riezky-gitH/OtoPonic/Dokumentasi/WhatsApp Image 2025-06-03 at 14.11.09_1a706787.jpg

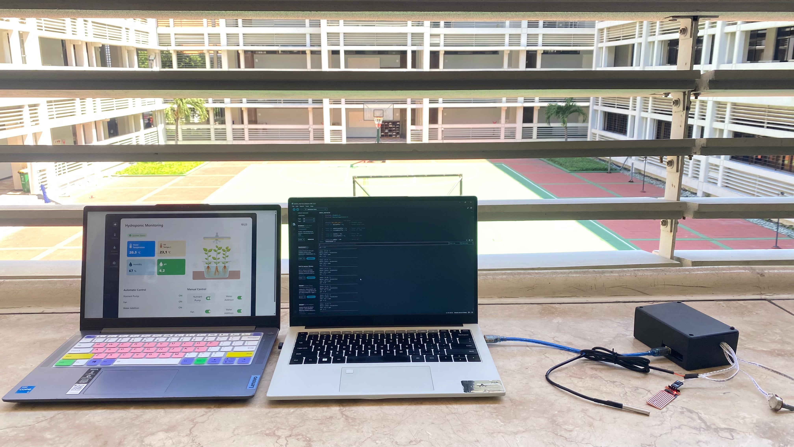
Dokumentasi/WhatsApp Image 2025-06-03 at 14.11.09_1a706787.jpg
